renaobrien/endgames-board/docs/screenshots/board-ai.png

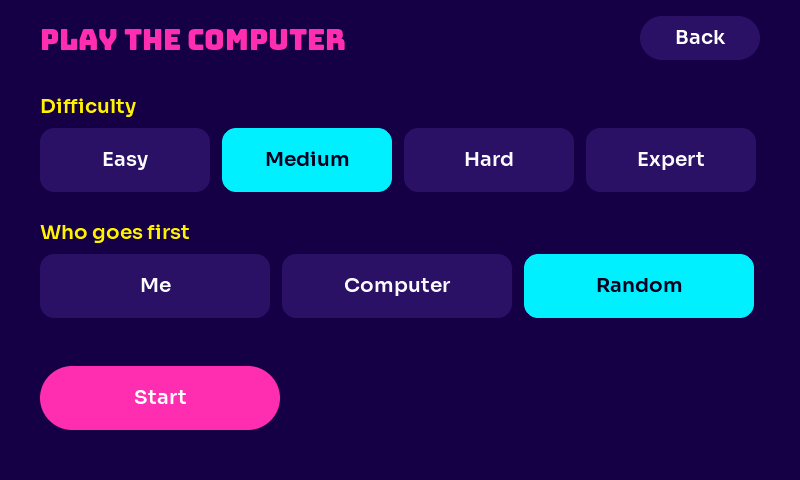
docs/screenshots/board-ai.png
