renaobrien/endgames-board/docs/screenshots/board-challenge.png

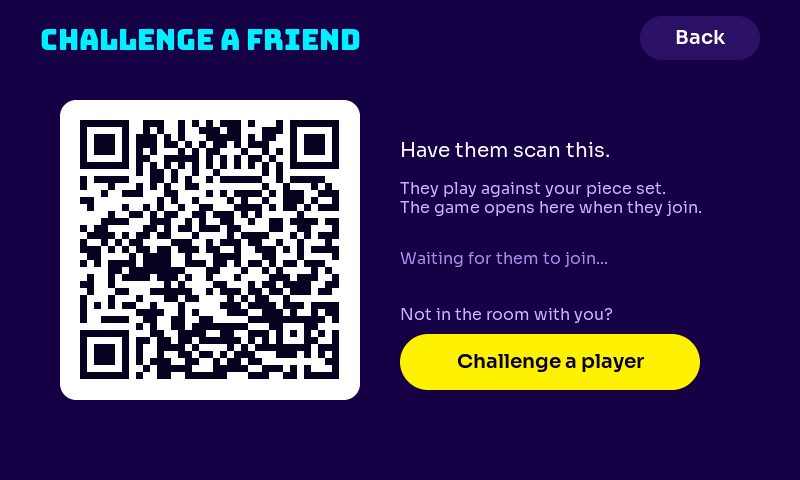
docs/screenshots/board-challenge.png
