renaobrien/endgames-board/docs/screenshots/board-game-timed-low.png

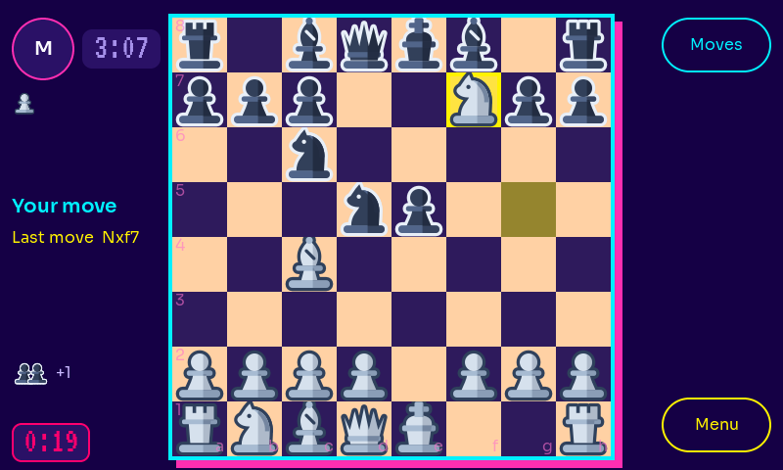
docs/screenshots/board-game-timed-low.png
