renaobrien/endgames-board/docs/screenshots/board-home.png

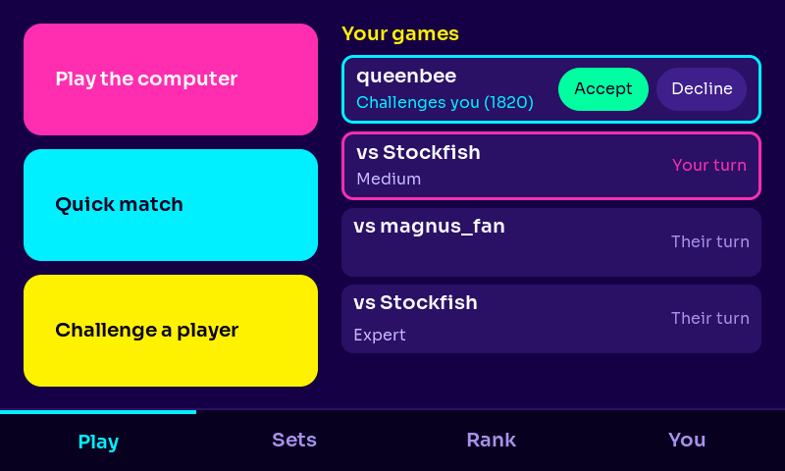
docs/screenshots/board-home.png
