renaobrien/endgames-board/docs/screenshots/board-idle.png

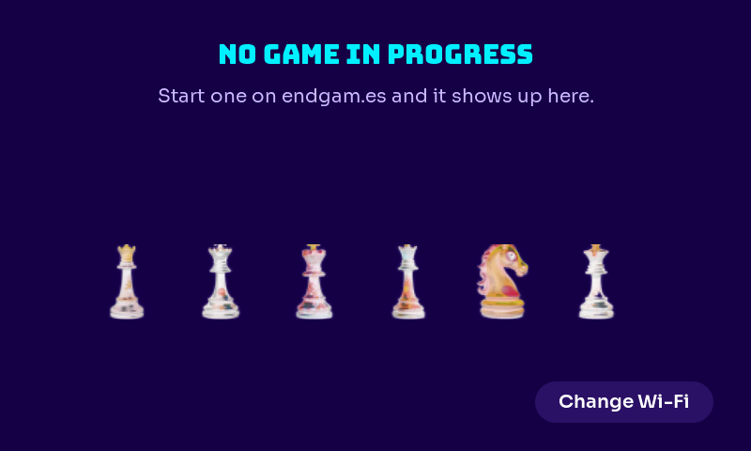
docs/screenshots/board-idle.png
