renaobrien/endgames-board/docs/screenshots/board-pair-1.png

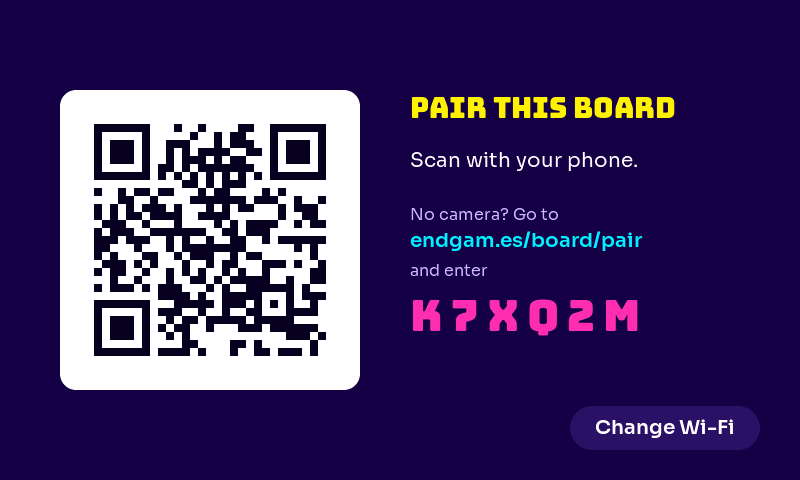
docs/screenshots/board-pair-1.png
