renaobrien/endgames-board/docs/screenshots/board-pair.png

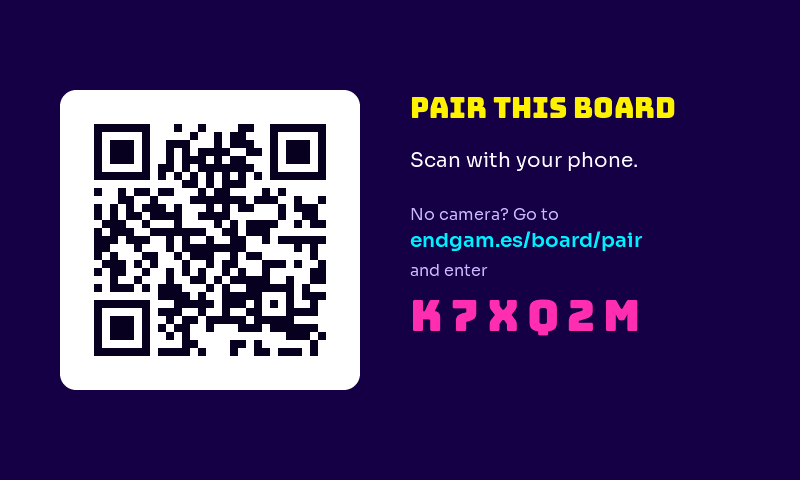
docs/screenshots/board-pair.png
