renaobrien/endgames-board/docs/screenshots/board-quick-none.png

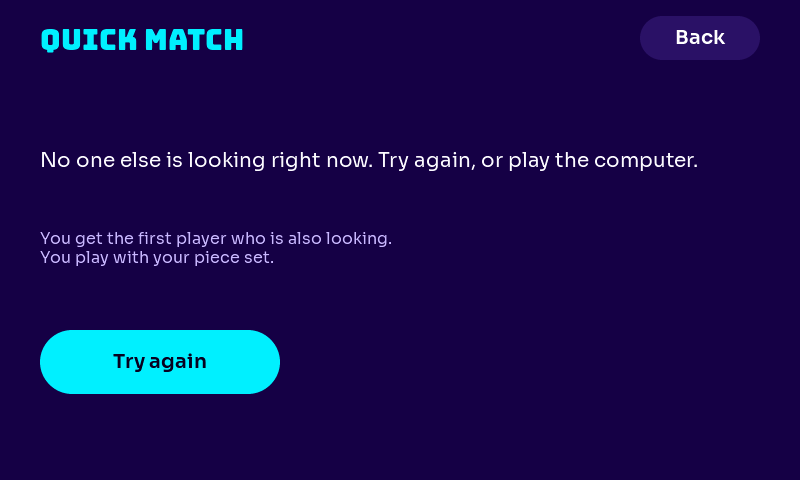
docs/screenshots/board-quick-none.png
