renaobrien/endgames-board/docs/screenshots/board-quick.png

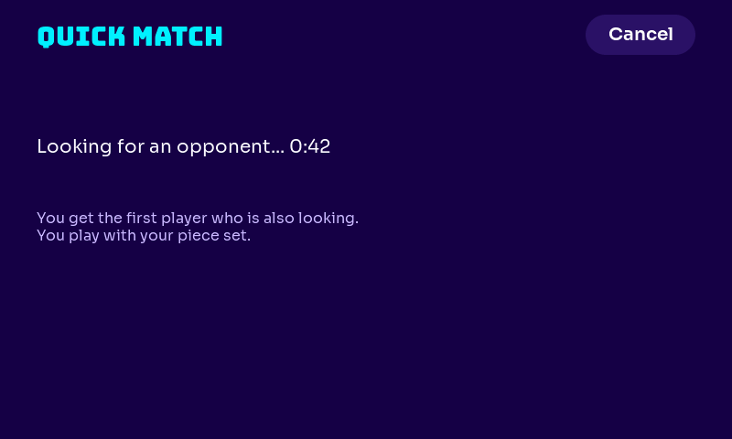
docs/screenshots/board-quick.png
