renaobrien/endgames-board/docs/screenshots/board-rank.png

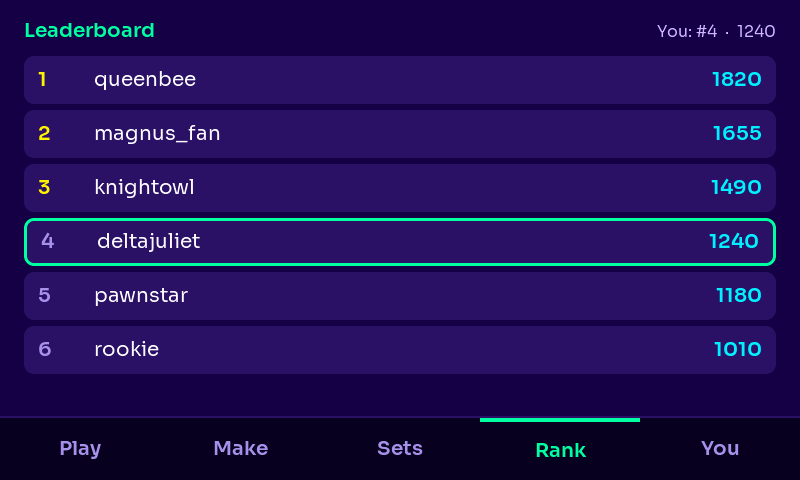
docs/screenshots/board-rank.png
