renaobrien/endgames-board/docs/screenshots/board-sets-edit.png

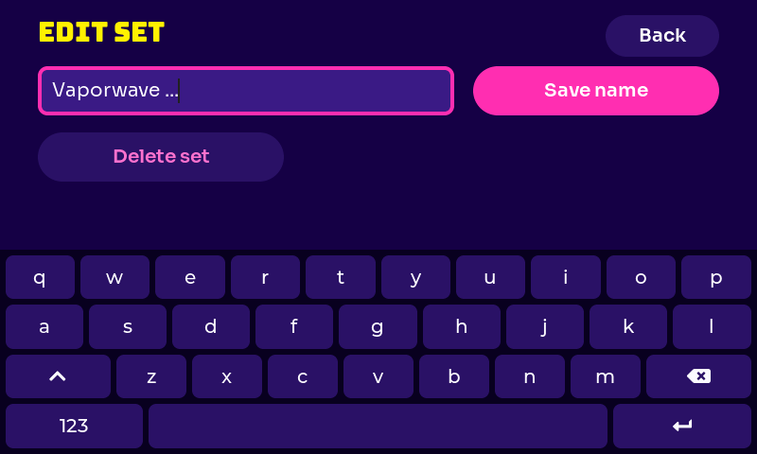
docs/screenshots/board-sets-edit.png
