renaobrien/endgames-board/docs/screenshots/board-sets-empty.png

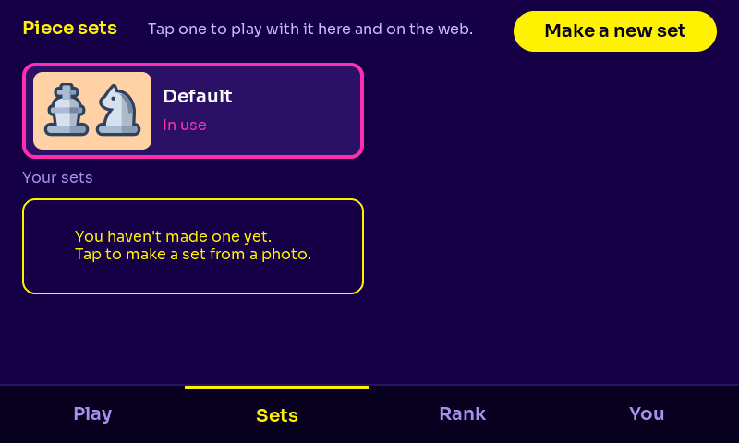
docs/screenshots/board-sets-empty.png
