renaobrien/endgames-board/docs/screenshots/board-sets.png

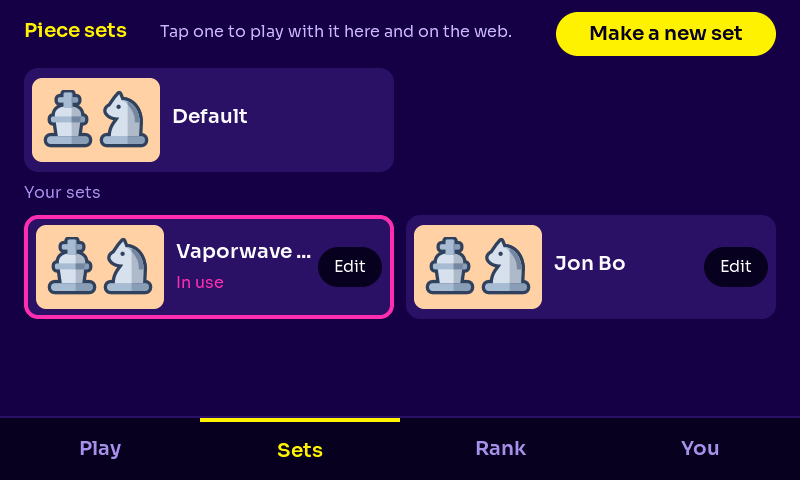
docs/screenshots/board-sets.png
