renaobrien/endgames-board/docs/screenshots/board-you.png

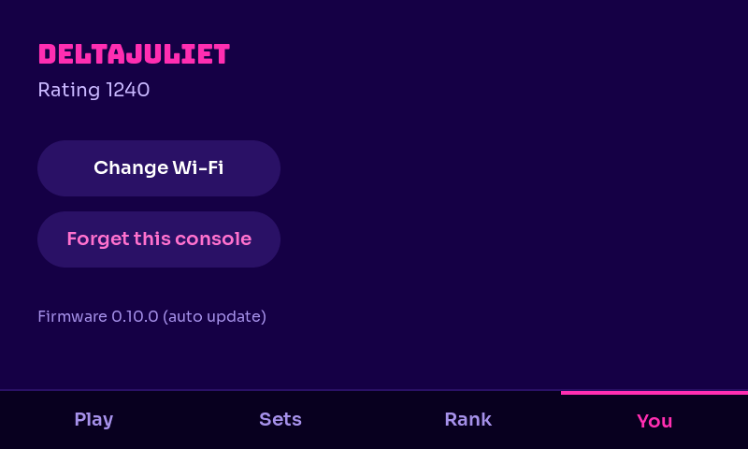
docs/screenshots/board-you.png
