renaobrien/endgames-board/docs/screenshots/side-by-side.png

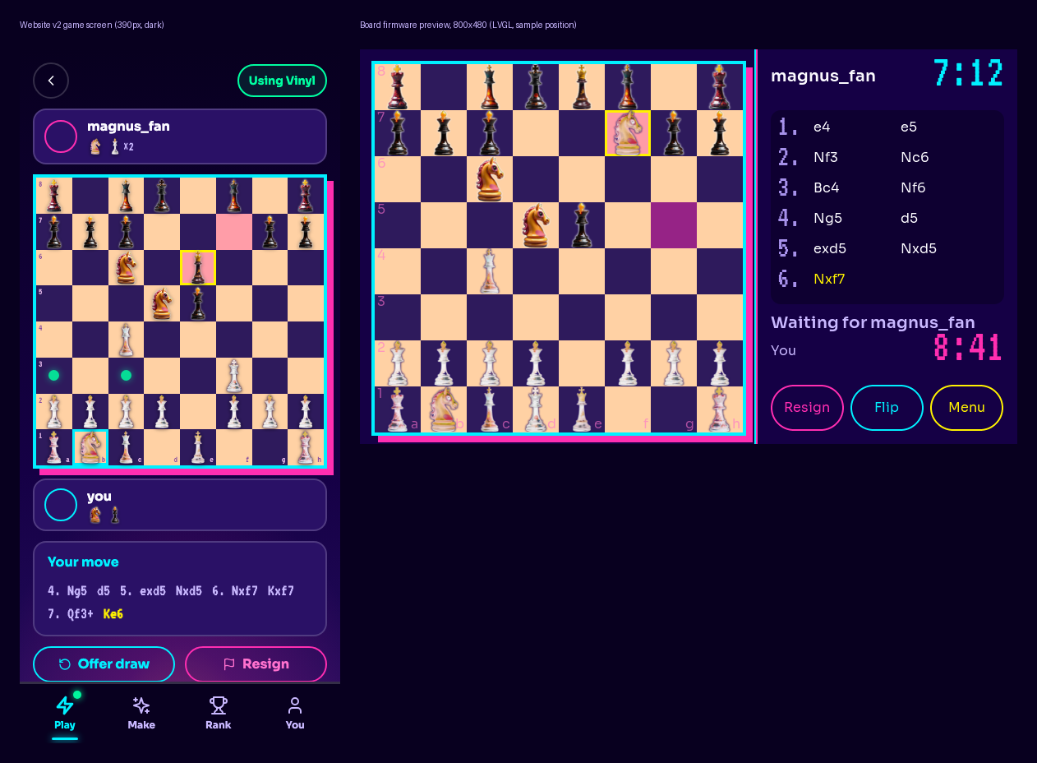
docs/screenshots/side-by-side.png
