renaobrien/endgames-board/docs/screenshots/website-game-390-dark.png

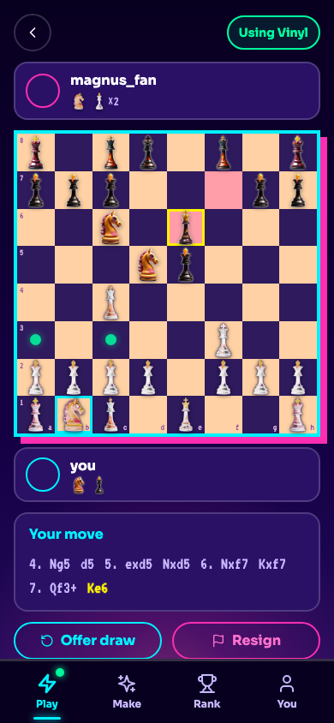
docs/screenshots/website-game-390-dark.png
