renaobrien/endgames-board/docs/screenshots/board-make.png

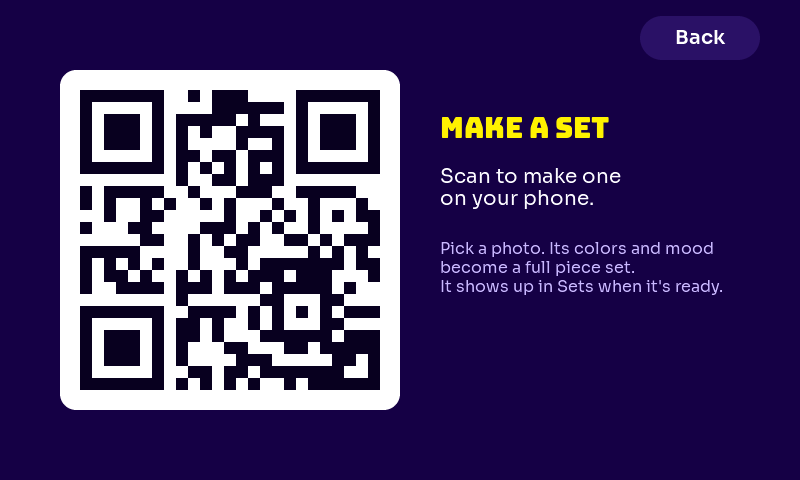
docs/screenshots/board-make.png
